evgs/mega-frank-u4/3d/JST_GH_1x02_P1.25mm.step

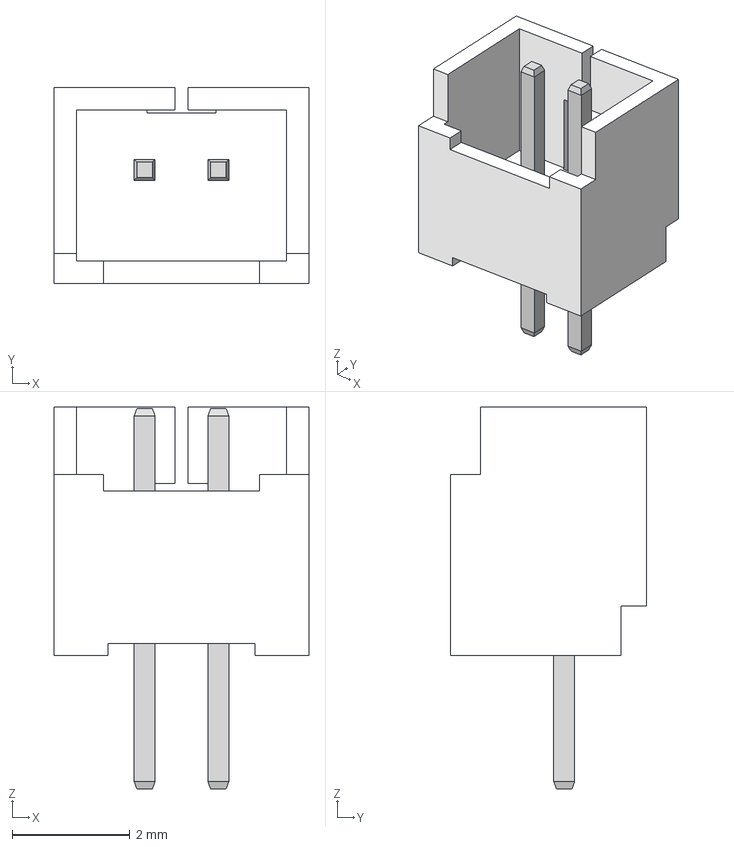
[picture p17: CAD file, 2026-07-08]
3d/JST_GH_1x02_P1.25mm.step
4.32 x 3.33 x 6.48 mm
