evgs/mega-frank-u4/3d/DIPSwitch_4pos_DS05.step

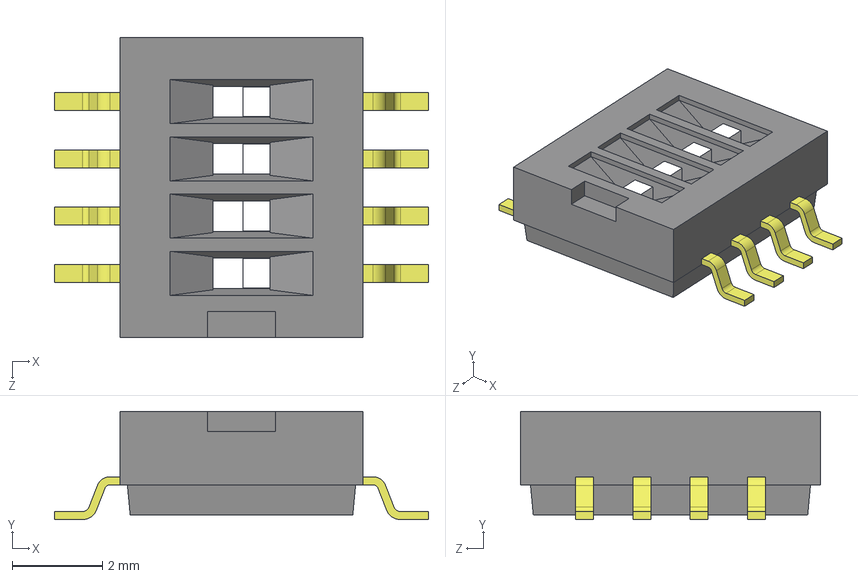
[picture p18: CAD file, 2026-07-08]
3d/DIPSwitch_4pos_DS05.step
8.30 x 2.40 x 6.65 mm
