evgs/mega-frank-u4/3d/C_0805_2012Metric.step

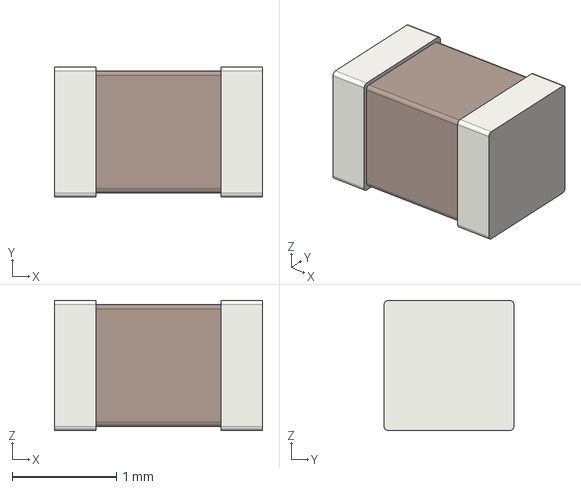
[picture p19: CAD file, 2026-07-08]
3d/C_0805_2012Metric.step
2.00 x 1.25 x 1.25 mm
