evgs/mega-frank-u4/3d/PinHeader_2x20_P2.54mm_Vertical.step

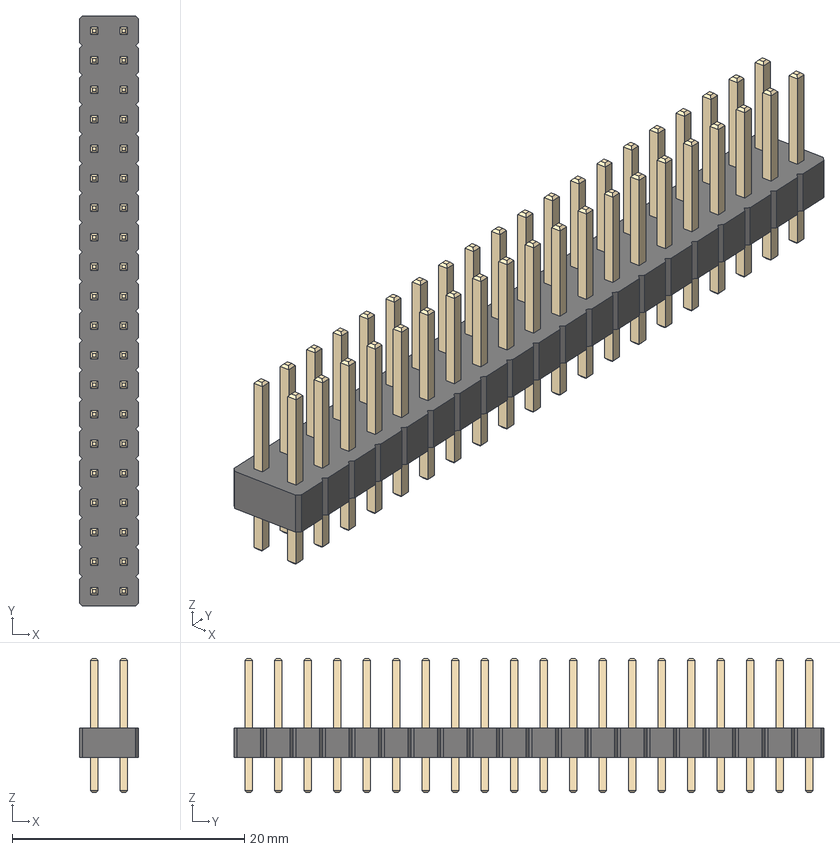
[picture p20: CAD file, 2026-07-08]
3d/PinHeader_2x20_P2.54mm_Vertical.step
5.08 x 50.8 x 11.5 mm
