evgs/mega-frank-u4/3d/JST_SH_1x03_P1.00mm_Vertical.step

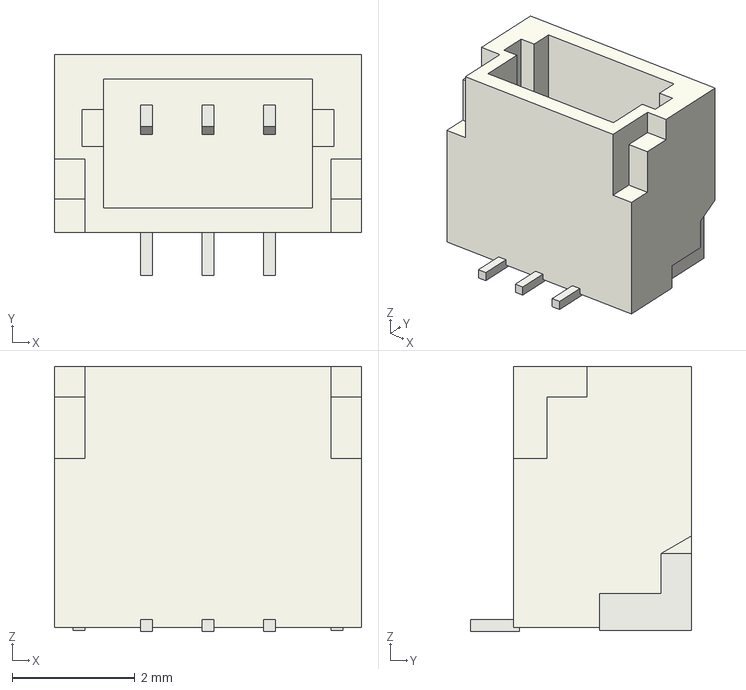
[picture p21: CAD file, 2026-07-08]
3d/JST_SH_1x03_P1.00mm_Vertical.step
5.00 x 3.60 x 4.32 mm
