evgs/mega-frank-u4/3d/AudioJack_3.5mm_PJ320D.step

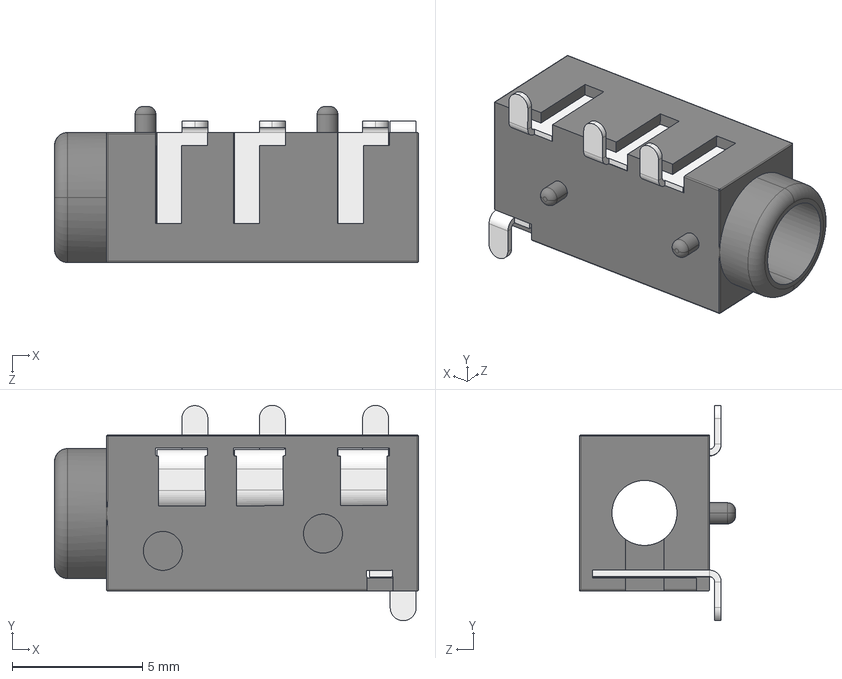
[picture p22: CAD file, 2026-07-08]
3d/AudioJack_3.5mm_PJ320D.step
14.0 x 8.28 x 6.00 mm
PJ320A
PJ320D-Pin x 3
PJ320D-Pin-B
