evgs/mega-frank-u4/3d/Switch_Slide_MSK12C02.step

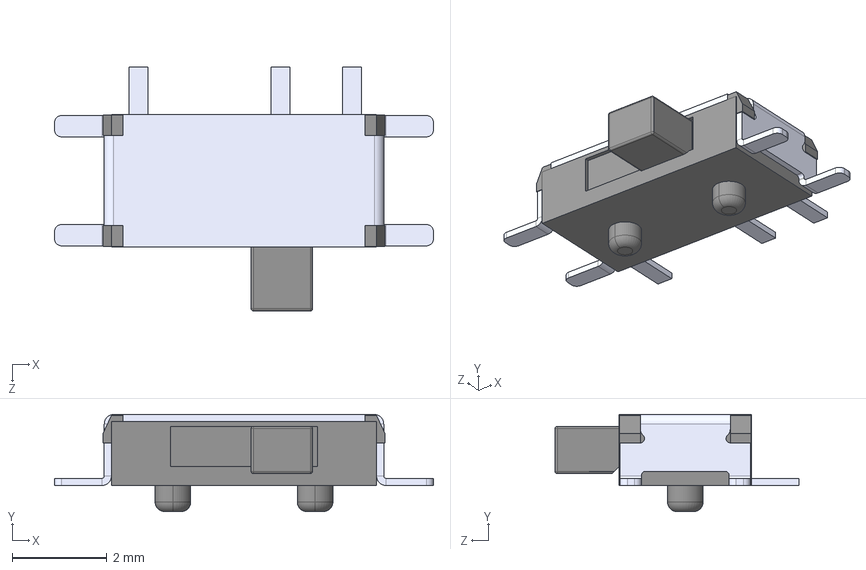
[picture p23: CAD file, 2026-07-08]
3d/Switch_Slide_MSK12C02.step
8.00 x 2.05 x 5.15 mm
