evgs/mega-frank-u4/3d/BarrelJack_DC-005.step

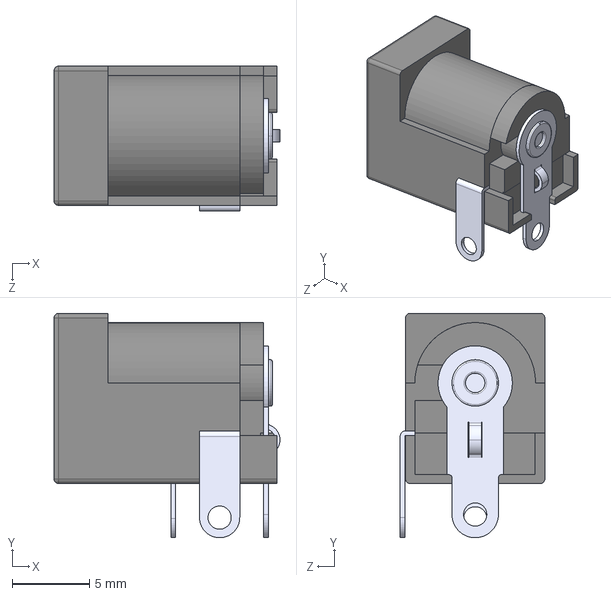
[picture p24: CAD file, 2026-07-08]
3d/BarrelJack_DC-005.step
14.6 x 14.5 x 9.35 mm
