evgs/mega-frank-u4/3d/DIP-40_W15.24mm_Socket.step

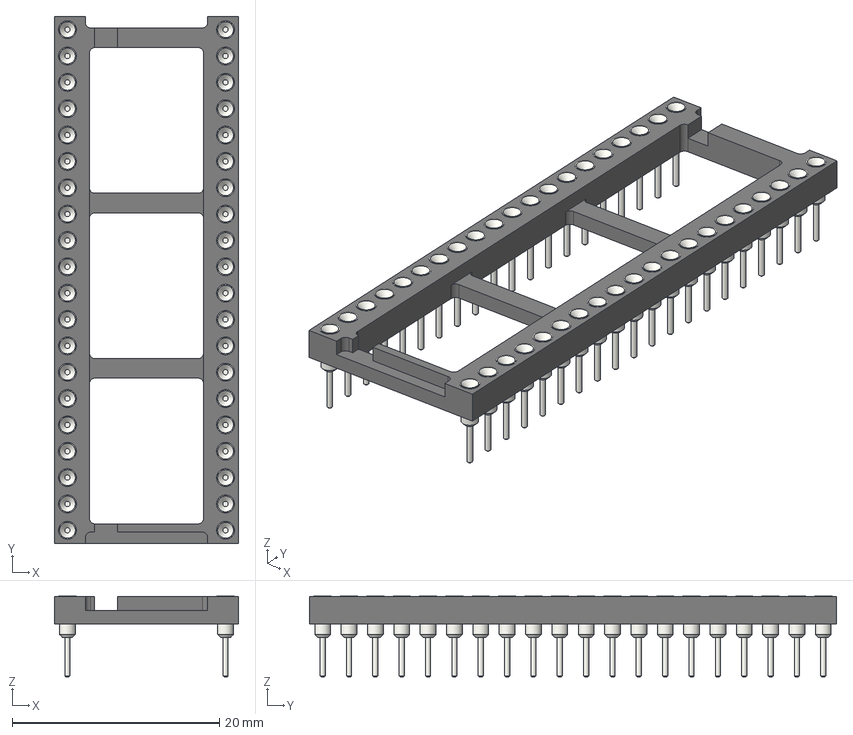
[picture p25: CAD file, 2026-07-08]
3d/DIP-40_W15.24mm_Socket.step
17.8 x 50.8 x 7.79 mm
