evgs/mega-frank-u4/3d/BarrelJack_RCJ-012.step

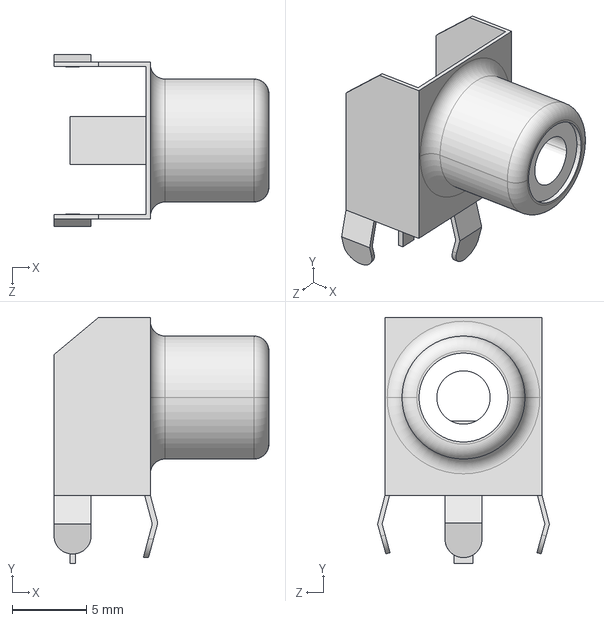
[picture p26: CAD file, 2026-07-08]
3d/BarrelJack_RCJ-012.step
14.5 x 16.6 x 11.6 mm
