evgs/mega-frank-u4/3d/MicroSD_SMD_Long.step

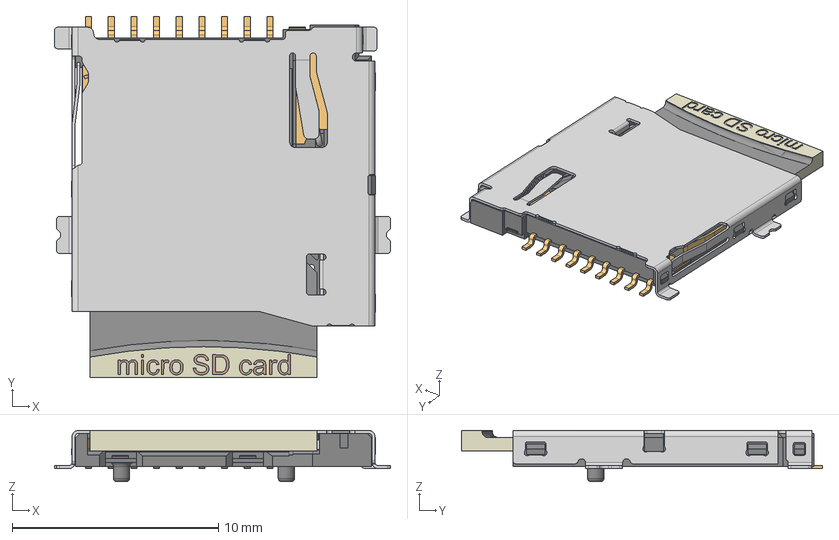
[picture p27: CAD file, 2026-07-08]
3d/MicroSD_SMD_Long.step
16.3 x 17.5 x 2.48 mm
693071020811_Housing
693071020811_Guide
693071020811_Spring
693071020811_Contact
693071020811_Hook
693071020811_Agraphe
693071020811_Shielding
MicroSD
