evgs/mega-frank-u4/3d/BAT-HLD-013-SMT-TR.step

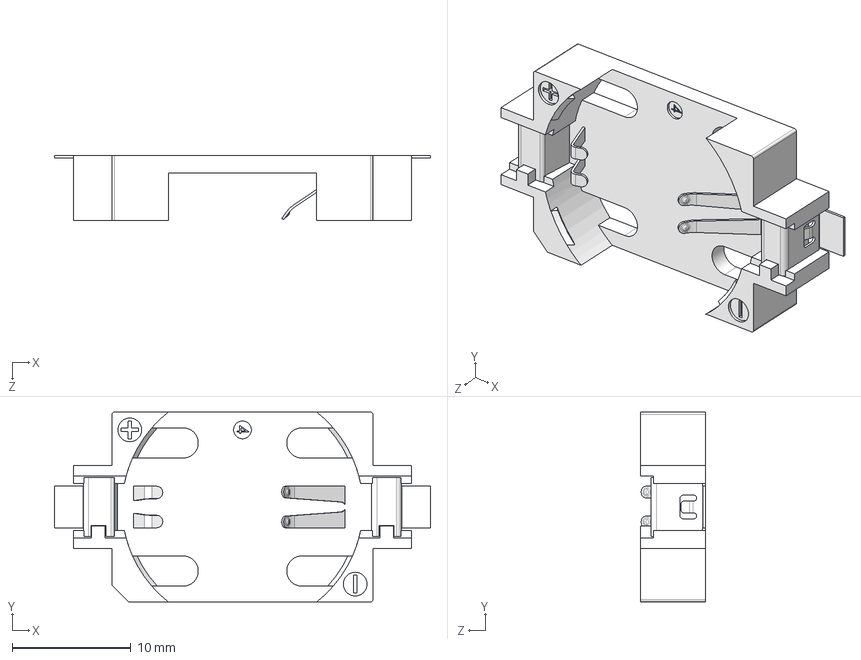
[picture p28: CAD file, 2026-07-08]
3d/BAT-HLD-013-SMT-TR.step
31.7 x 16.0 x 5.50 mm
