evgs/mega-frank-u4/3d/D_SMA.step

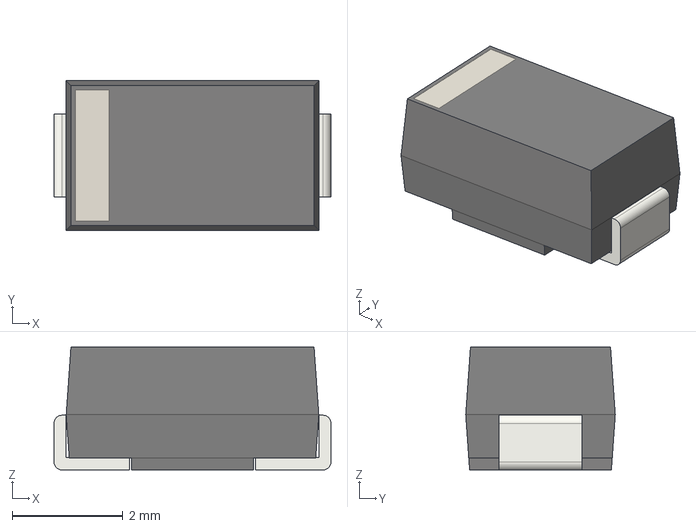
[picture p29: CAD file, 2026-07-08]
3d/D_SMA.step
5.00 x 2.70 x 2.22 mm
