evgs/mega-frank-u4/3d/DSUB-9_Male_TopMount.step

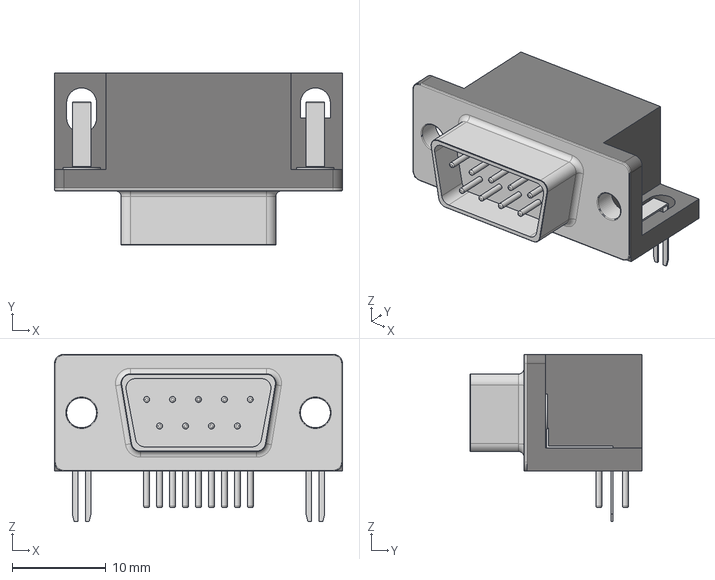
[picture p30: CAD file, 2026-07-08]
3d/DSUB-9_Male_TopMount.step
30.8 x 18.4 x 17.9 mm
