evgs/mega-frank-u4/3d/PinHeader_2x20_P2.54mm.step

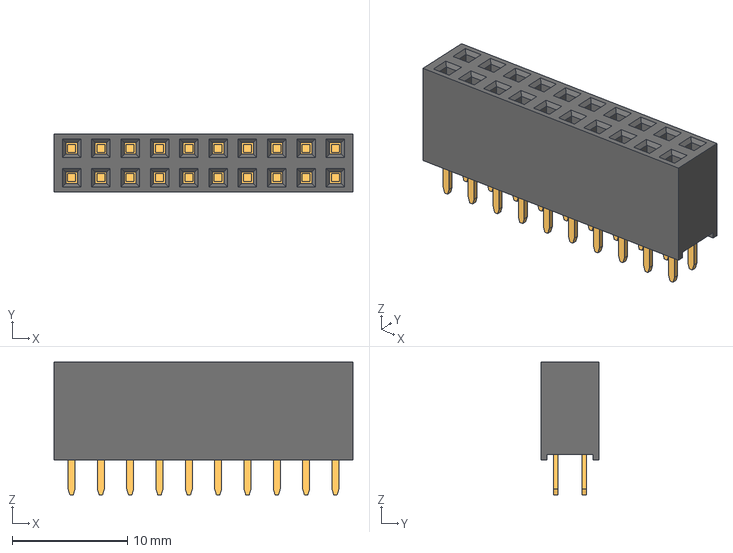
[picture p31: CAD file, 2026-07-08]
3d/PinHeader_2x20_P2.54mm.step
25.9 x 5.00 x 11.5 mm
