evgs/mega-frank-u4/3d/MiniDIN_6pin_Female.step

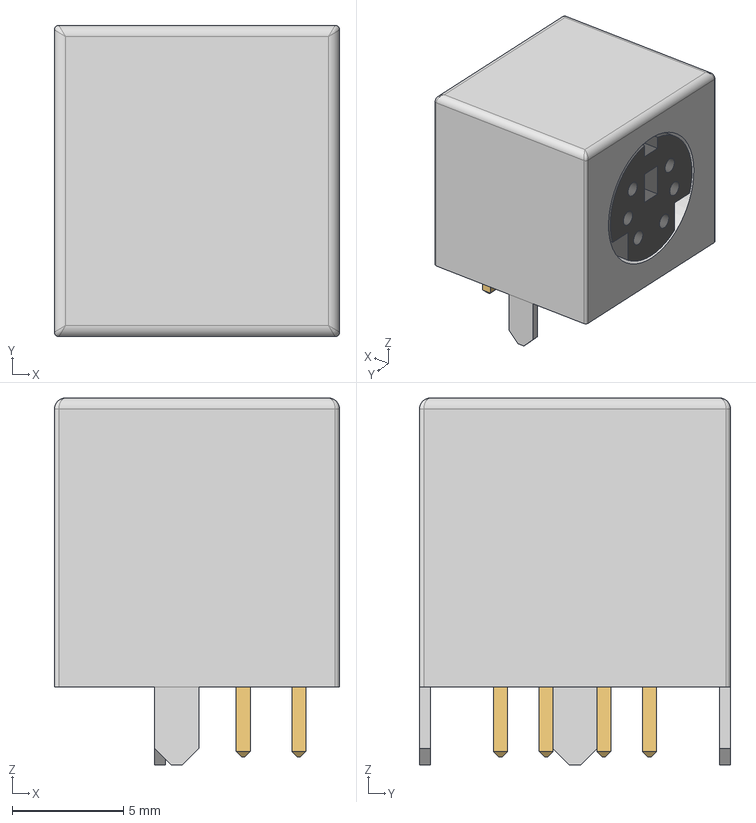
[picture p32: CAD file, 2026-07-08]
3d/MiniDIN_6pin_Female.step
12.8 x 14.0 x 16.5 mm
