evgs/mega-frank-u4/3d/LED_0805.step

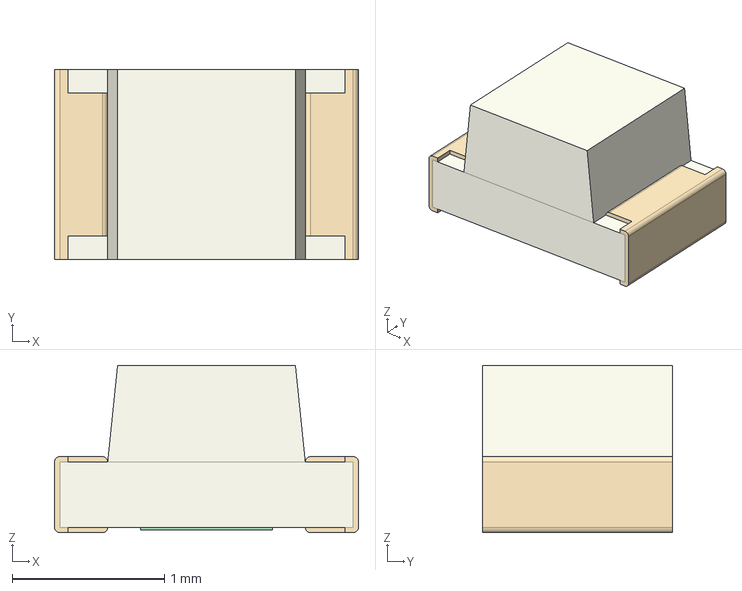
[picture p33: CAD file, 2026-07-08]
3d/LED_0805.step
2.00 x 1.25 x 1.10 mm
