evgs/mega-frank-u4/3d/USB_C_Receptacle.step

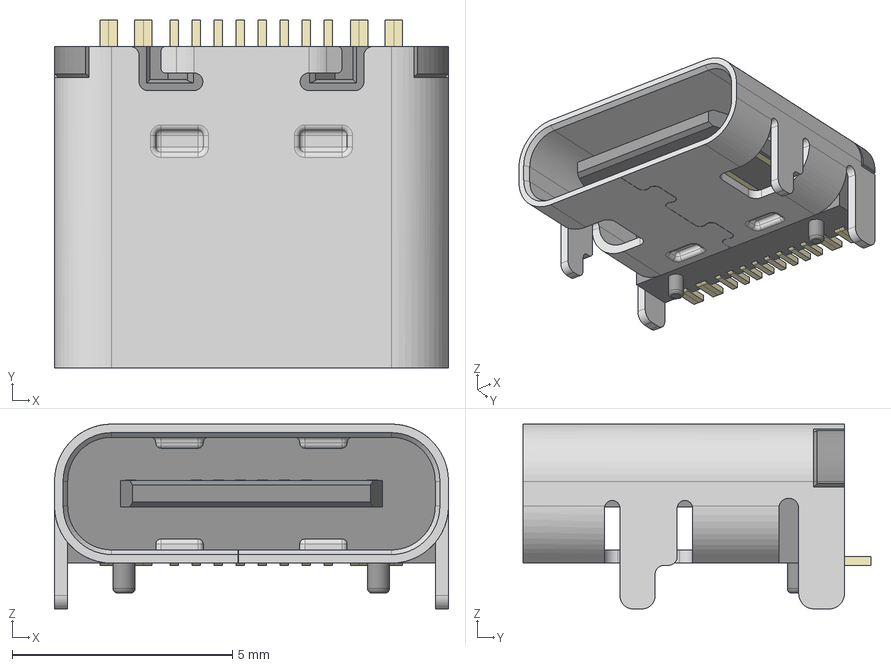
[picture p34: CAD file, 2026-07-08]
3d/USB_C_Receptacle.step
8.95 x 7.90 x 4.20 mm
