evgs/mega-frank-u4/3d/SOIC-8_3.9x4.9mm_P1.27mm.step

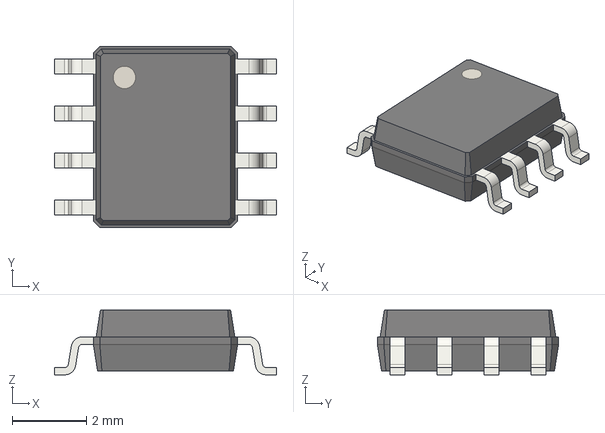
[picture p36: CAD file, 2026-07-08]
3d/SOIC-8_3.9x4.9mm_P1.27mm.step
6.00 x 4.90 x 1.75 mm
