evgs/mega-frank-u4/3d/USB_A_Stacked.step

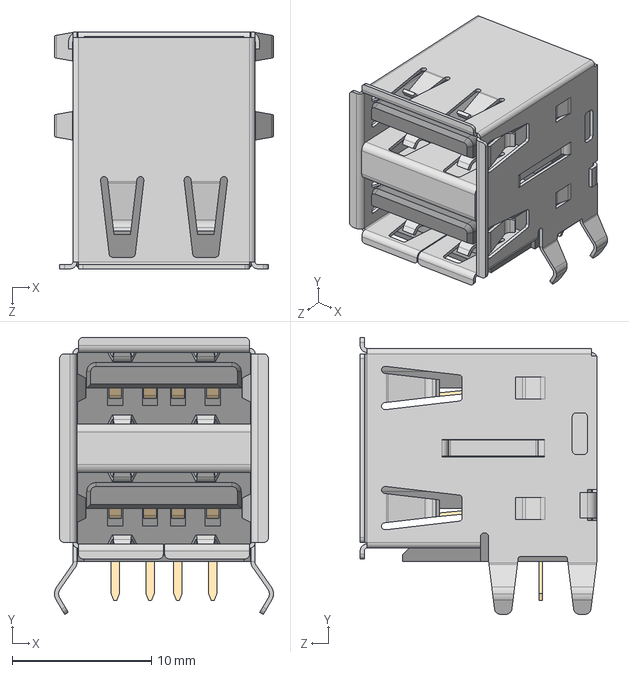
[picture p37: CAD file, 2026-07-08]
3d/USB_A_Stacked.step
15.7 x 19.9 x 17.0 mm
