evgs/mega-frank-u4/3d/SOIC-14_P1.27mm.step

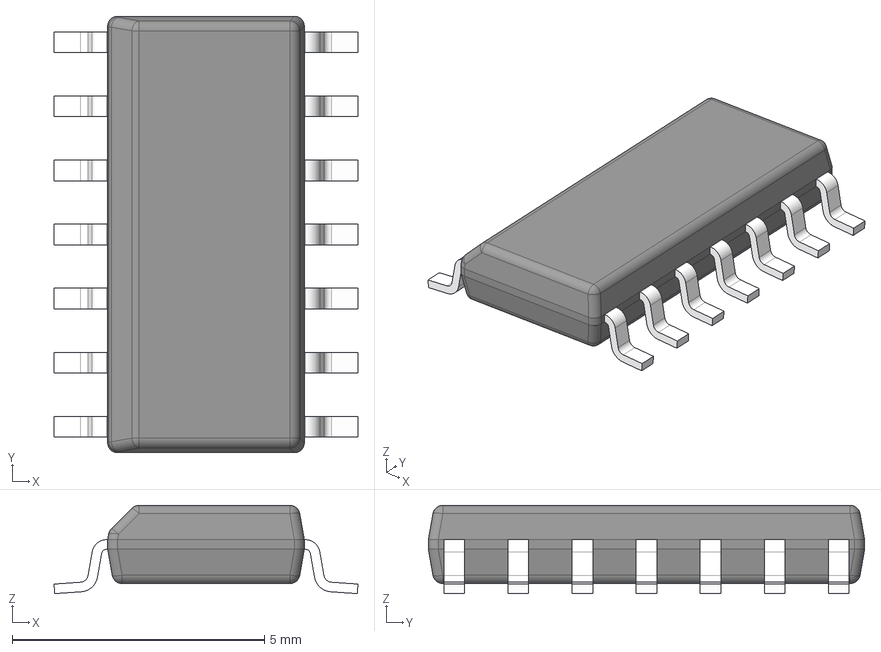
[picture p38: CAD file, 2026-07-08]
3d/SOIC-14_P1.27mm.step
6.03 x 8.65 x 1.75 mm
BODY-SO
LEAD-SO x 14
PIN1-ID
