evgs/mega-frank-u4/3d/SOIC-9_P1.27mm.step

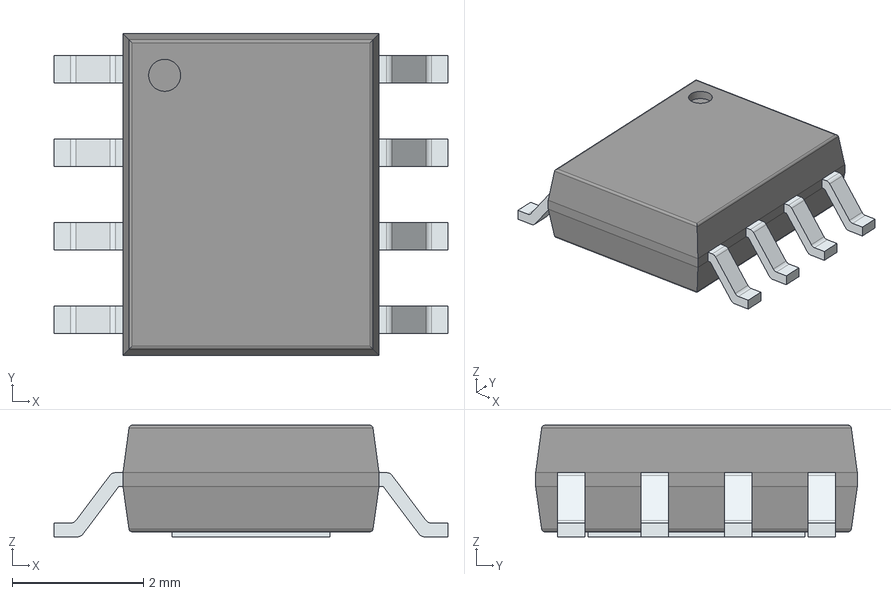
[picture p39: CAD file, 2026-07-08]
3d/SOIC-9_P1.27mm.step
6.00 x 4.90 x 1.70 mm
PinsArrayLR
ThermalPad
