evgs/mega-frank-u4/3d/Battery_CR1220.step

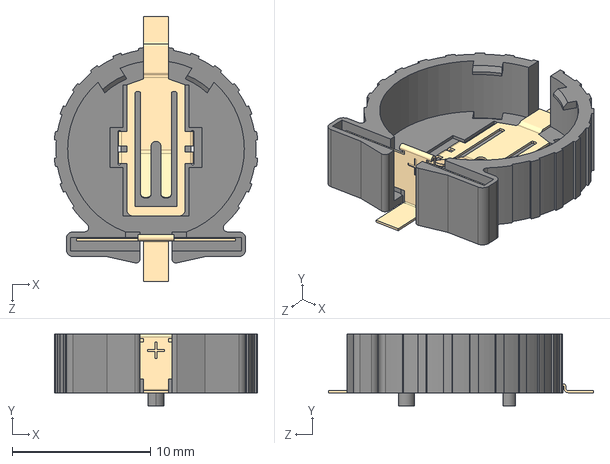
[picture p40: CAD file, 2026-07-08]
3d/Battery_CR1220.step
14.7 x 5.20 x 19.2 mm
