evgs/mega-frank-u4/3d/PinHeader_2x06_P2.54mm.step

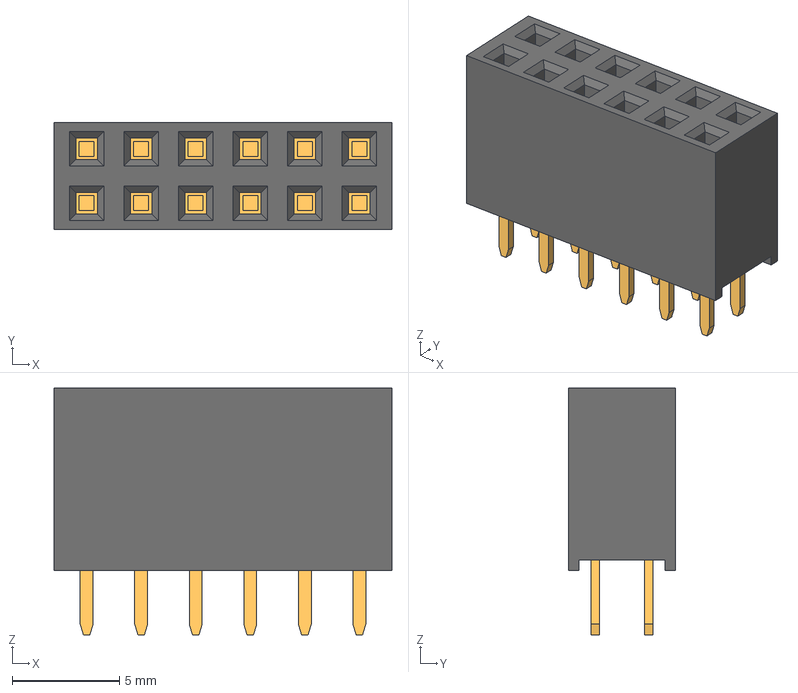
[picture p41: CAD file, 2026-07-08]
3d/PinHeader_2x06_P2.54mm.step
15.7 x 5.00 x 11.5 mm
