evgs/mega-frank-u4/3d/DSUB-15_Female.step

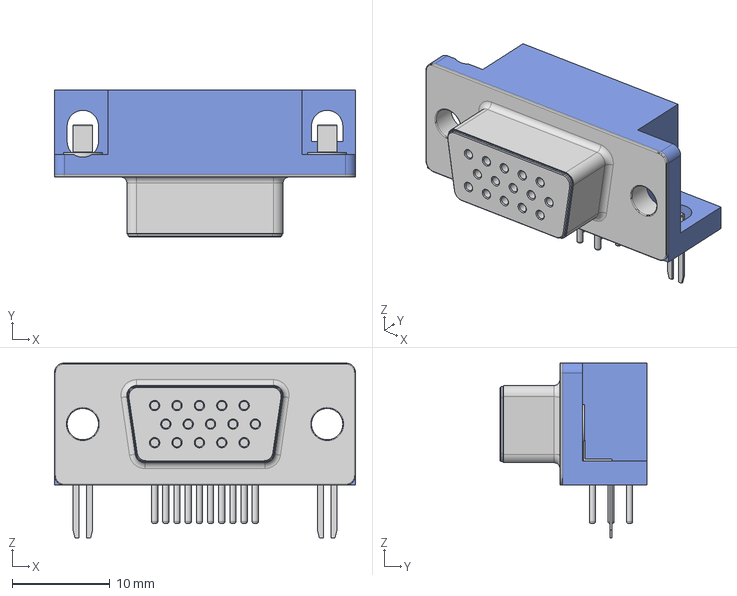
[picture p42: CAD file, 2026-07-08]
3d/DSUB-15_Female.step
30.8 x 15.0 x 17.9 mm
