evgs/mega-frank-u4/3d/Inductor_CDRH104RNP.step

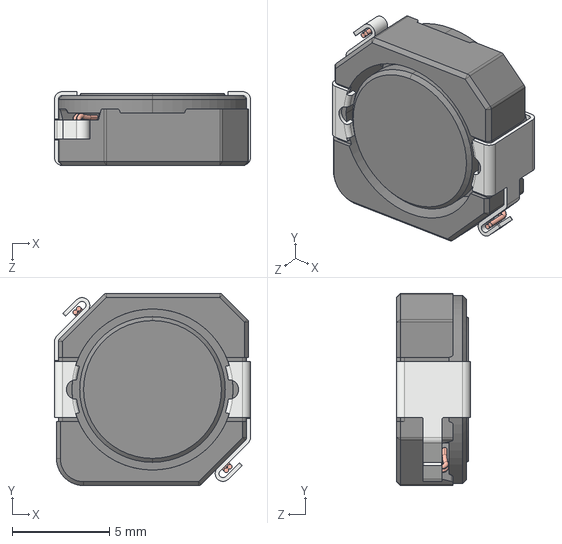
[picture p43: CAD file, 2026-07-08]
3d/Inductor_CDRH104RNP.step
10.1 x 9.90 x 3.80 mm
