evgs/mega-frank-u4/3d/SOT-23.step

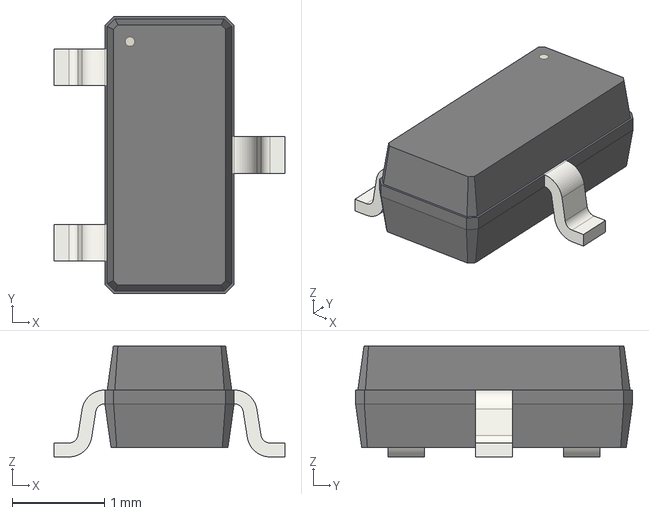
[picture p44: CAD file, 2026-07-08]
3d/SOT-23.step
2.50 x 3.00 x 1.20 mm
