evgs/mega-frank-u4/3d/CP_Radial_D4.0mm_P1.50mm.step

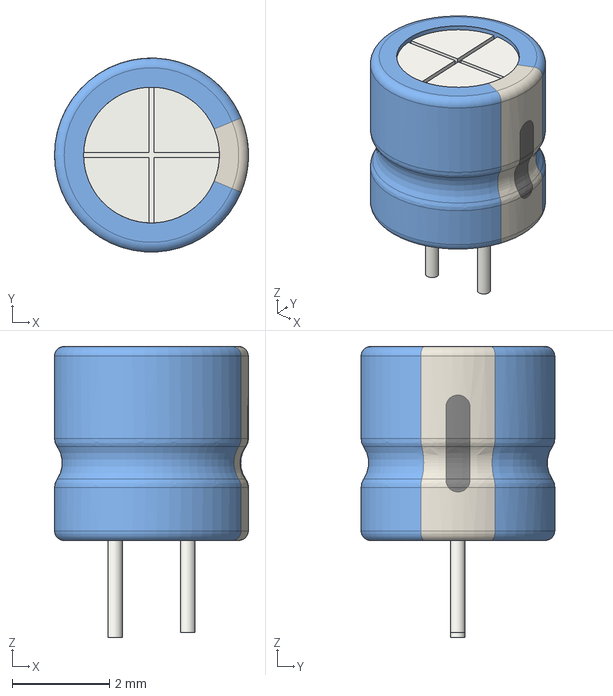
[picture p45: CAD file, 2026-07-08]
3d/CP_Radial_D4.0mm_P1.50mm.step
4.00 x 4.00 x 6.00 mm
