evgs/mega-frank-u4/3d/C_Radial_D6.3mm_P2.50mm.step

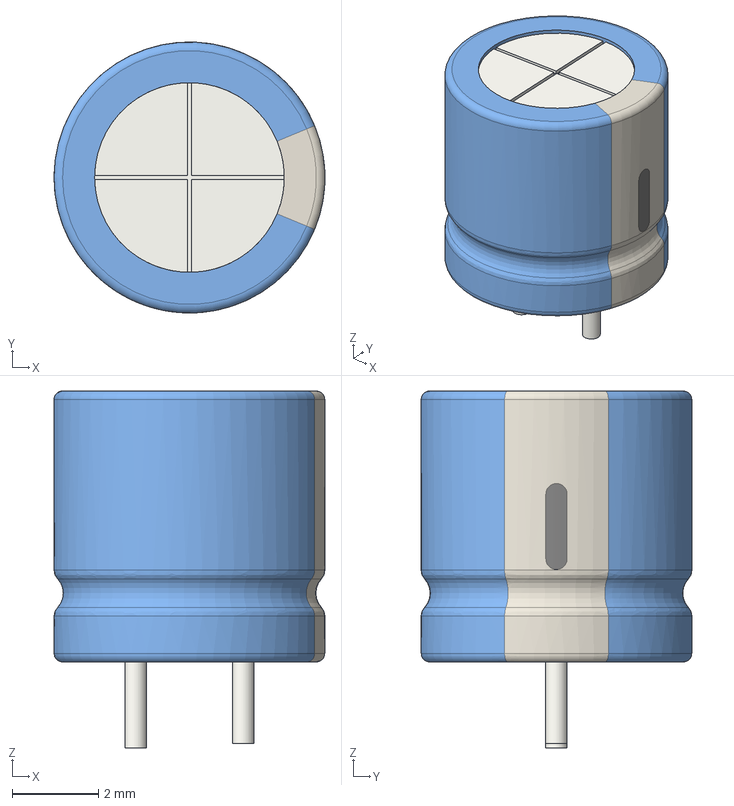
[picture p46: CAD file, 2026-07-08]
3d/C_Radial_D6.3mm_P2.50mm.step
6.30 x 6.30 x 8.30 mm
