evgs/mega-frank-u4/3d/DS2401P+.stp

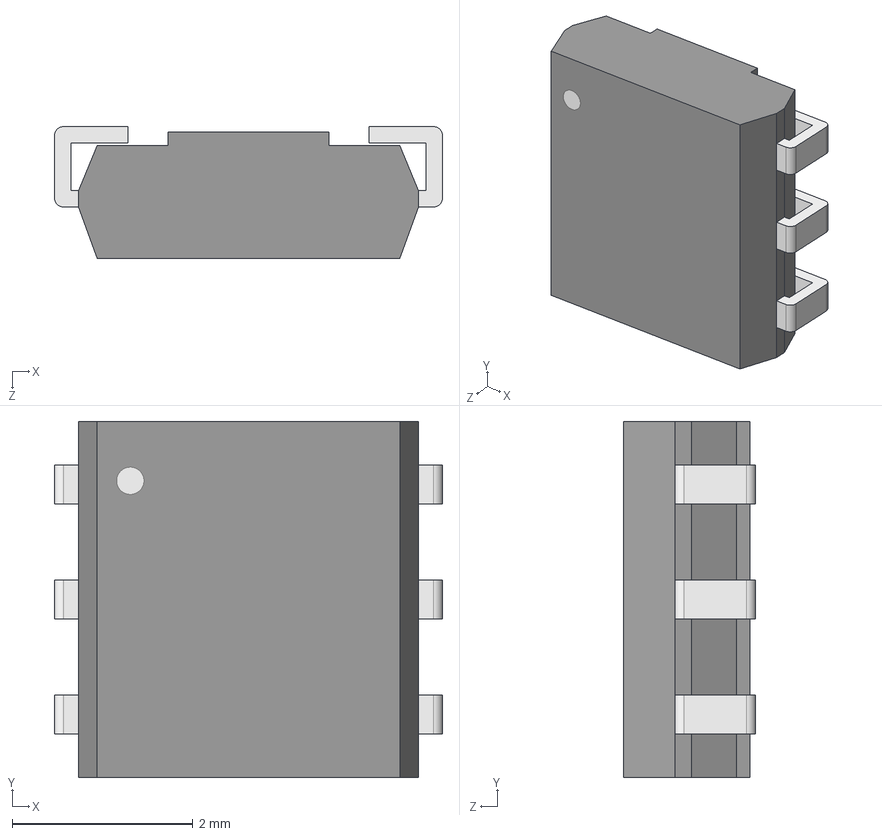
[picture p47: CAD file, 2026-07-08]
3d/DS2401P+.stp
4.29 x 3.94 x 1.46 mm
