evgs/mega-frank-u4/3d/D_MiniMELF.step

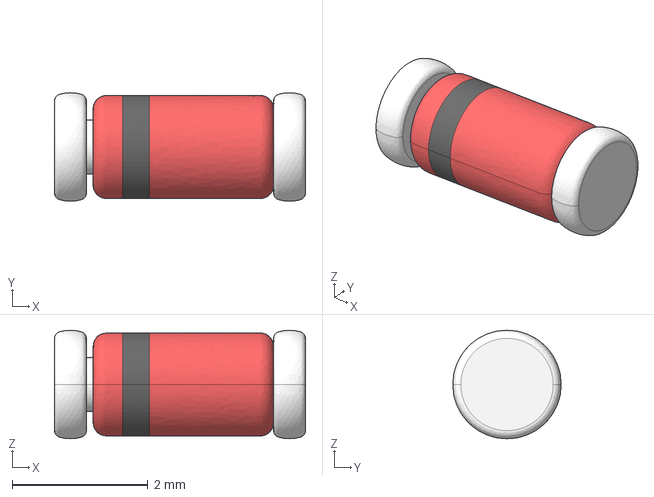
[picture p48: CAD file, 2026-07-08]
3d/D_MiniMELF.step
3.70 x 1.60 x 1.60 mm
