evgs/mega-frank-u4/3d/HDMI_Female.step

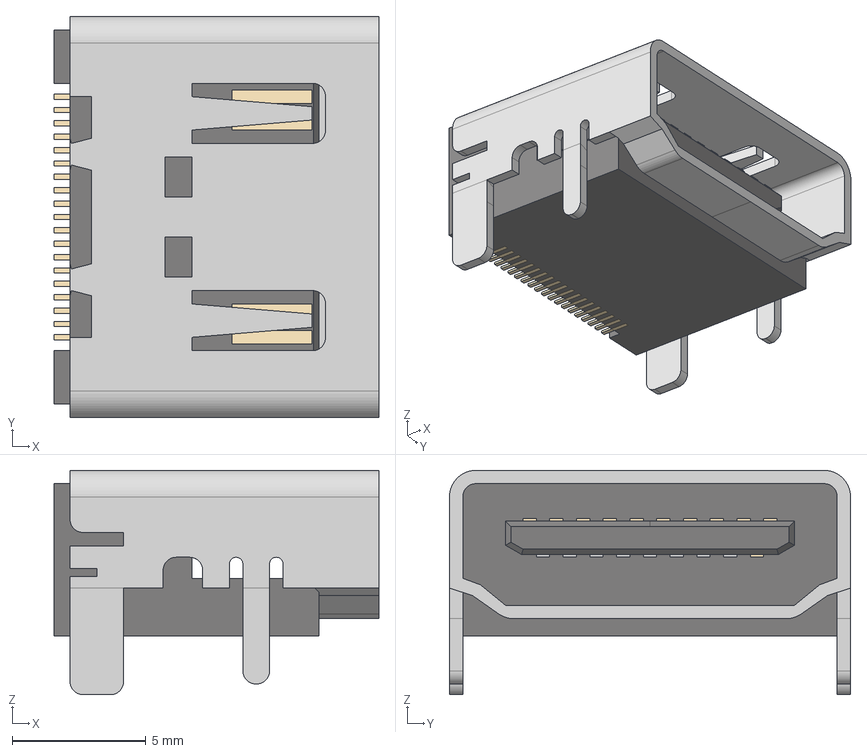
[picture p49: CAD file, 2026-07-08]
3d/HDMI_Female.step
12.2 x 15.0 x 8.39 mm
