evgs/mega-frank-u4/3d/PinHeader_1x03_P2.54mm.step

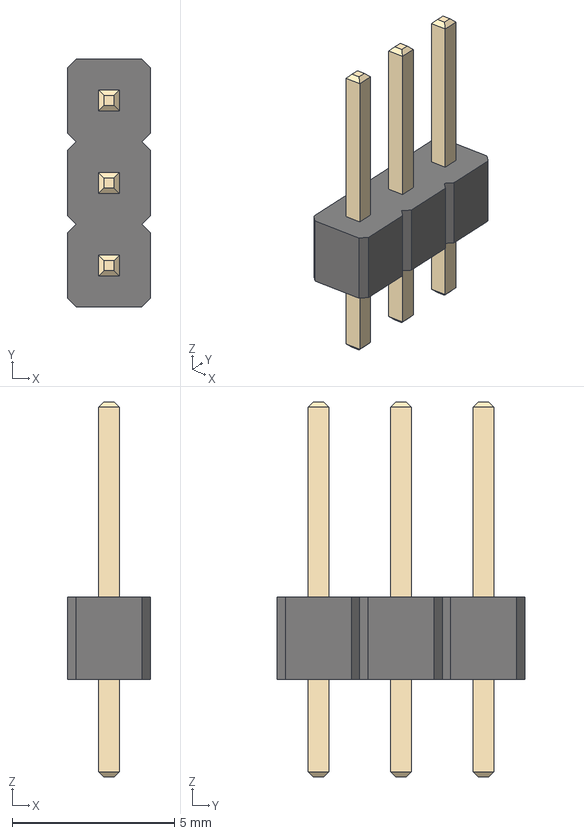
[picture p50: CAD file, 2026-07-08]
3d/PinHeader_1x03_P2.54mm.step
2.54 x 7.62 x 11.5 mm
