evgs/mega-frank-u4/3d/DS01-254-S-06BE.step

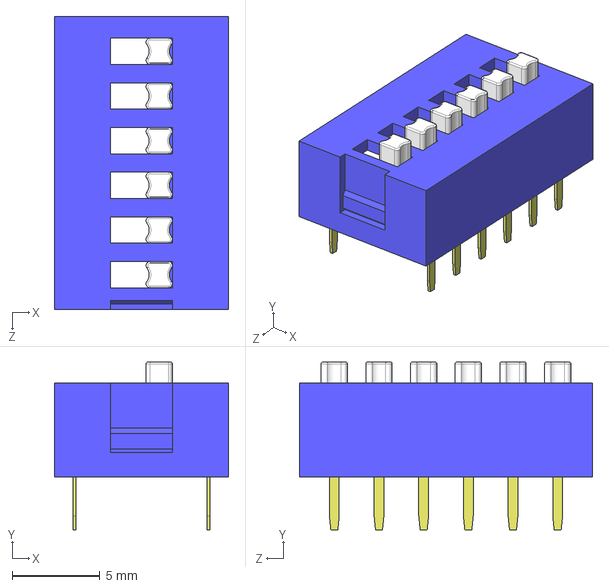
[picture p51: CAD file, 2026-07-08]
3d/DS01-254-S-06BE.step
9.90 x 9.55 x 16.7 mm
