evgs/mega-frank-u4/3d/D_SOD-323.step

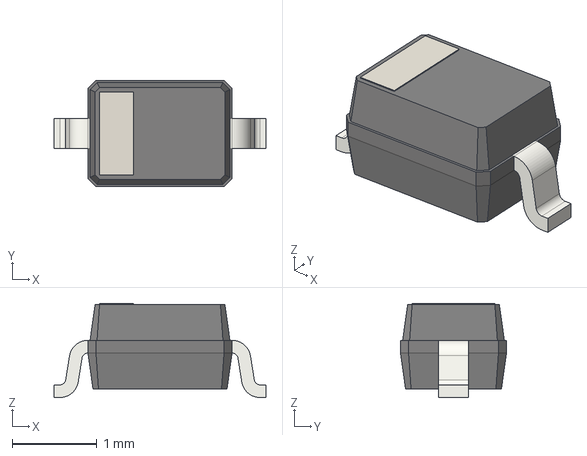
[picture p52: CAD file, 2026-07-08]
3d/D_SOD-323.step
2.50 x 1.25 x 1.11 mm
