evgs/mega-frank-u4/3d/PinHeader_2x04_P2.54mm.step

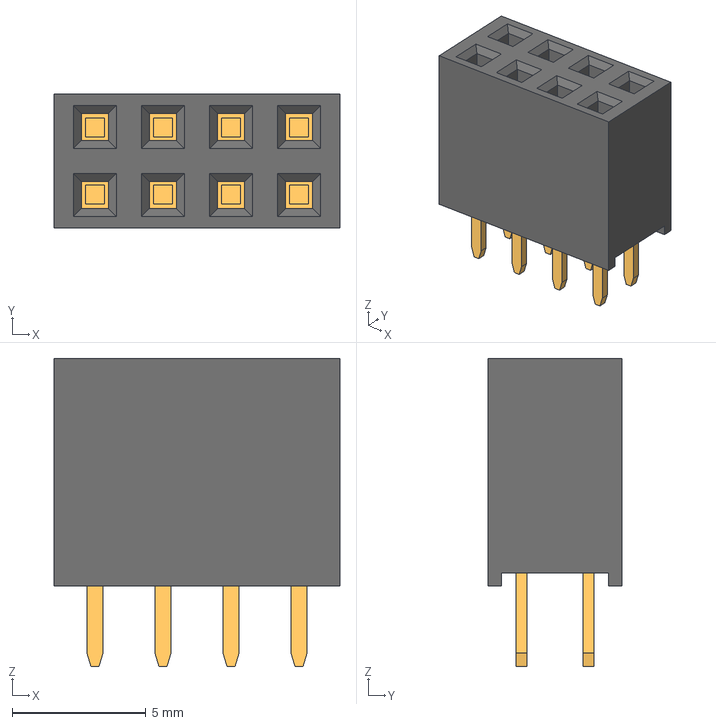
[picture p53: CAD file, 2026-07-08]
3d/PinHeader_2x04_P2.54mm.step
10.7 x 5.00 x 11.5 mm
