evgs/mega-frank-u4/3d/Crystal_HC49-S.step

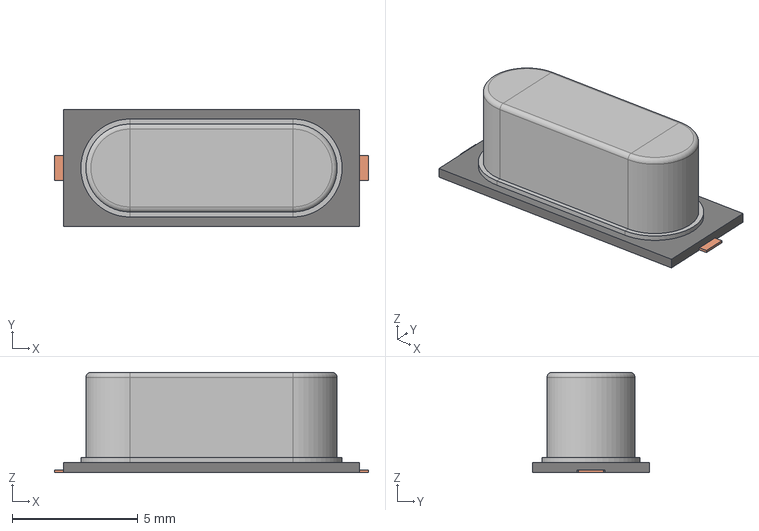
[picture p54: CAD file, 2026-07-08]
3d/Crystal_HC49-S.step
12.5 x 4.65 x 4.00 mm
